Joe-Purvis/UFE/Upduino/Simulink/Scripts/WR_RegisterStressTest_Log_2026-01-09_093914.csv

timestamp | pass | pattern | idx | addr | tx | rx | status | result | reason | attempt | phase | bytes_scanned | frames_rejected | port_reopened
2026-01-09 09:39:15.129 | 1 | INC | 1 | 0x30 | 0x00 | 0x00 | 0x00 | PASS | OK | 1 | 1 | 1 | 0 | 0
2026-01-09 09:39:15.221 | 1 | INC | 2 | 0x30 | 0x01 | 0x01 | 0x00 | PASS | OK | 1 | 1 | 1 | 0 | 0
2026-01-09 09:39:15.301 | 1 | INC | 3 | 0x30 | 0x02 | 0x02 | 0x00 | PASS | OK | 1 | 1 | 1 | 0 | 0
2026-01-09 09:39:15.379 | 1 | INC | 4 | 0x30 | 0x03 | 0x03 | 0x00 | PASS | OK | 1 | 1 | 1 | 0 | 0
2026-01-09 09:39:15.459 | 1 | INC | 5 | 0x30 | 0x04 | 0x04 | 0x00 | PASS | OK | 1 | 1 | 1 | 0 | 0
2026-01-09 09:39:15.537 | 1 | INC | 6 | 0x30 | 0x05 | 0x05 | 0x00 | PASS | OK | 1 | 1 | 1 | 0 | 0
2026-01-09 09:39:15.615 | 1 | INC | 7 | 0x30 | 0x06 | 0x06 | 0x00 | PASS | OK | 1 | 1 | 1 | 0 | 0
2026-01-09 09:39:15.695 | 1 | INC | 8 | 0x30 | 0x07 | 0x07 | 0x00 | PASS | OK | 1 | 1 | 1 | 0 | 0
2026-01-09 09:39:15.775 | 1 | INC | 9 | 0x30 | 0x08 | 0x08 | 0x00 | PASS | OK | 1 | 1 | 1 | 0 | 0
2026-01-09 09:39:15.853 | 1 | INC | 10 | 0x30 | 0x09 | 0x09 | 0x00 | PASS | OK | 1 | 1 | 1 | 0 | 0
2026-01-09 09:39:15.933 | 1 | INC | 11 | 0x30 | 0x0A | 0x0A | 0x00 | PASS | OK | 1 | 1 | 1 | 0 | 0
2026-01-09 09:39:16.012 | 1 | INC | 12 | 0x30 | 0x0B | 0x0B | 0x00 | PASS | OK | 1 | 1 | 1 | 0 | 0
2026-01-09 09:39:16.105 | 1 | INC | 13 | 0x30 | 0x0C | 0x0C | 0x00 | PASS | OK | 1 | 1 | 1 | 0 | 0
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
2026-01-09 09:40:57.224 | 2 | DEC | 154 | 0x30 | 0x66 | 0x66 | 0x00 | PASS | OK | 1 | 1 | 1 | 0 | 0
2026-01-09 09:40:57.302 | 2 | DEC | 155 | 0x30 | 0x65 | 0x65 | 0x00 | PASS | OK | 1 | 1 | 1 | 0 | 0
2026-01-09 09:40:57.380 | 2 | DEC | 156 | 0x30 | 0x64 | 0x64 | 0x00 | PASS | OK | 1 | 1 | 1 | 0 | 0
2026-01-09 09:40:57.460 | 2 | DEC | 157 | 0x30 | 0x63 | 0x63 | 0x00 | PASS | OK | 1 | 1 | 1 | 0 | 0
2026-01-09 09:40:57.540 | 2 | DEC | 158 | 0x30 | 0x62 | 0x62 | 0x00 | PASS | OK | 1 | 1 | 1 | 0 | 0
2026-01-09 09:40:57.633 | 2 | DEC | 159 | 0x30 | 0x61 | 0x61 | 0x00 | PASS | OK | 1 | 1 | 1 | 0 | 0
2026-01-09 09:40:57.700 | 2 | DEC | 160 | 0x30 | 0x60 | 0x60 | 0x00 | PASS | OK | 1 | 1 | 1 | 0 | 0
2026-01-09 09:40:57.790 | 2 | DEC | 161 | 0x30 | 0x5F | 0x5F | 0x00 | PASS | OK | 1 | 1 | 1 | 0 | 0
2026-01-09 09:40:57.866 | 2 | DEC | 162 | 0x30 | 0x5E | 0x5E | 0x00 | PASS | OK | 1 | 1 | 1 | 0 | 0
2026-01-09 09:40:57.944 | 2 | DEC | 163 | 0x30 | 0x5D | 0x5D | 0x00 | PASS | OK | 1 | 1 | 1 | 0 | 0
2026-01-09 09:40:58.022 | 2 | DEC | 164 | 0x30 | 0x5C | 0x5C | 0x00 | PASS | OK | 1 | 1 | 1 | 0 | 0
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
